DovydasTEDS/teds-kb-100/pcb/kb.kicad_sch

## KiCad design pcb/kb.kicad_sch (2026-01-30)

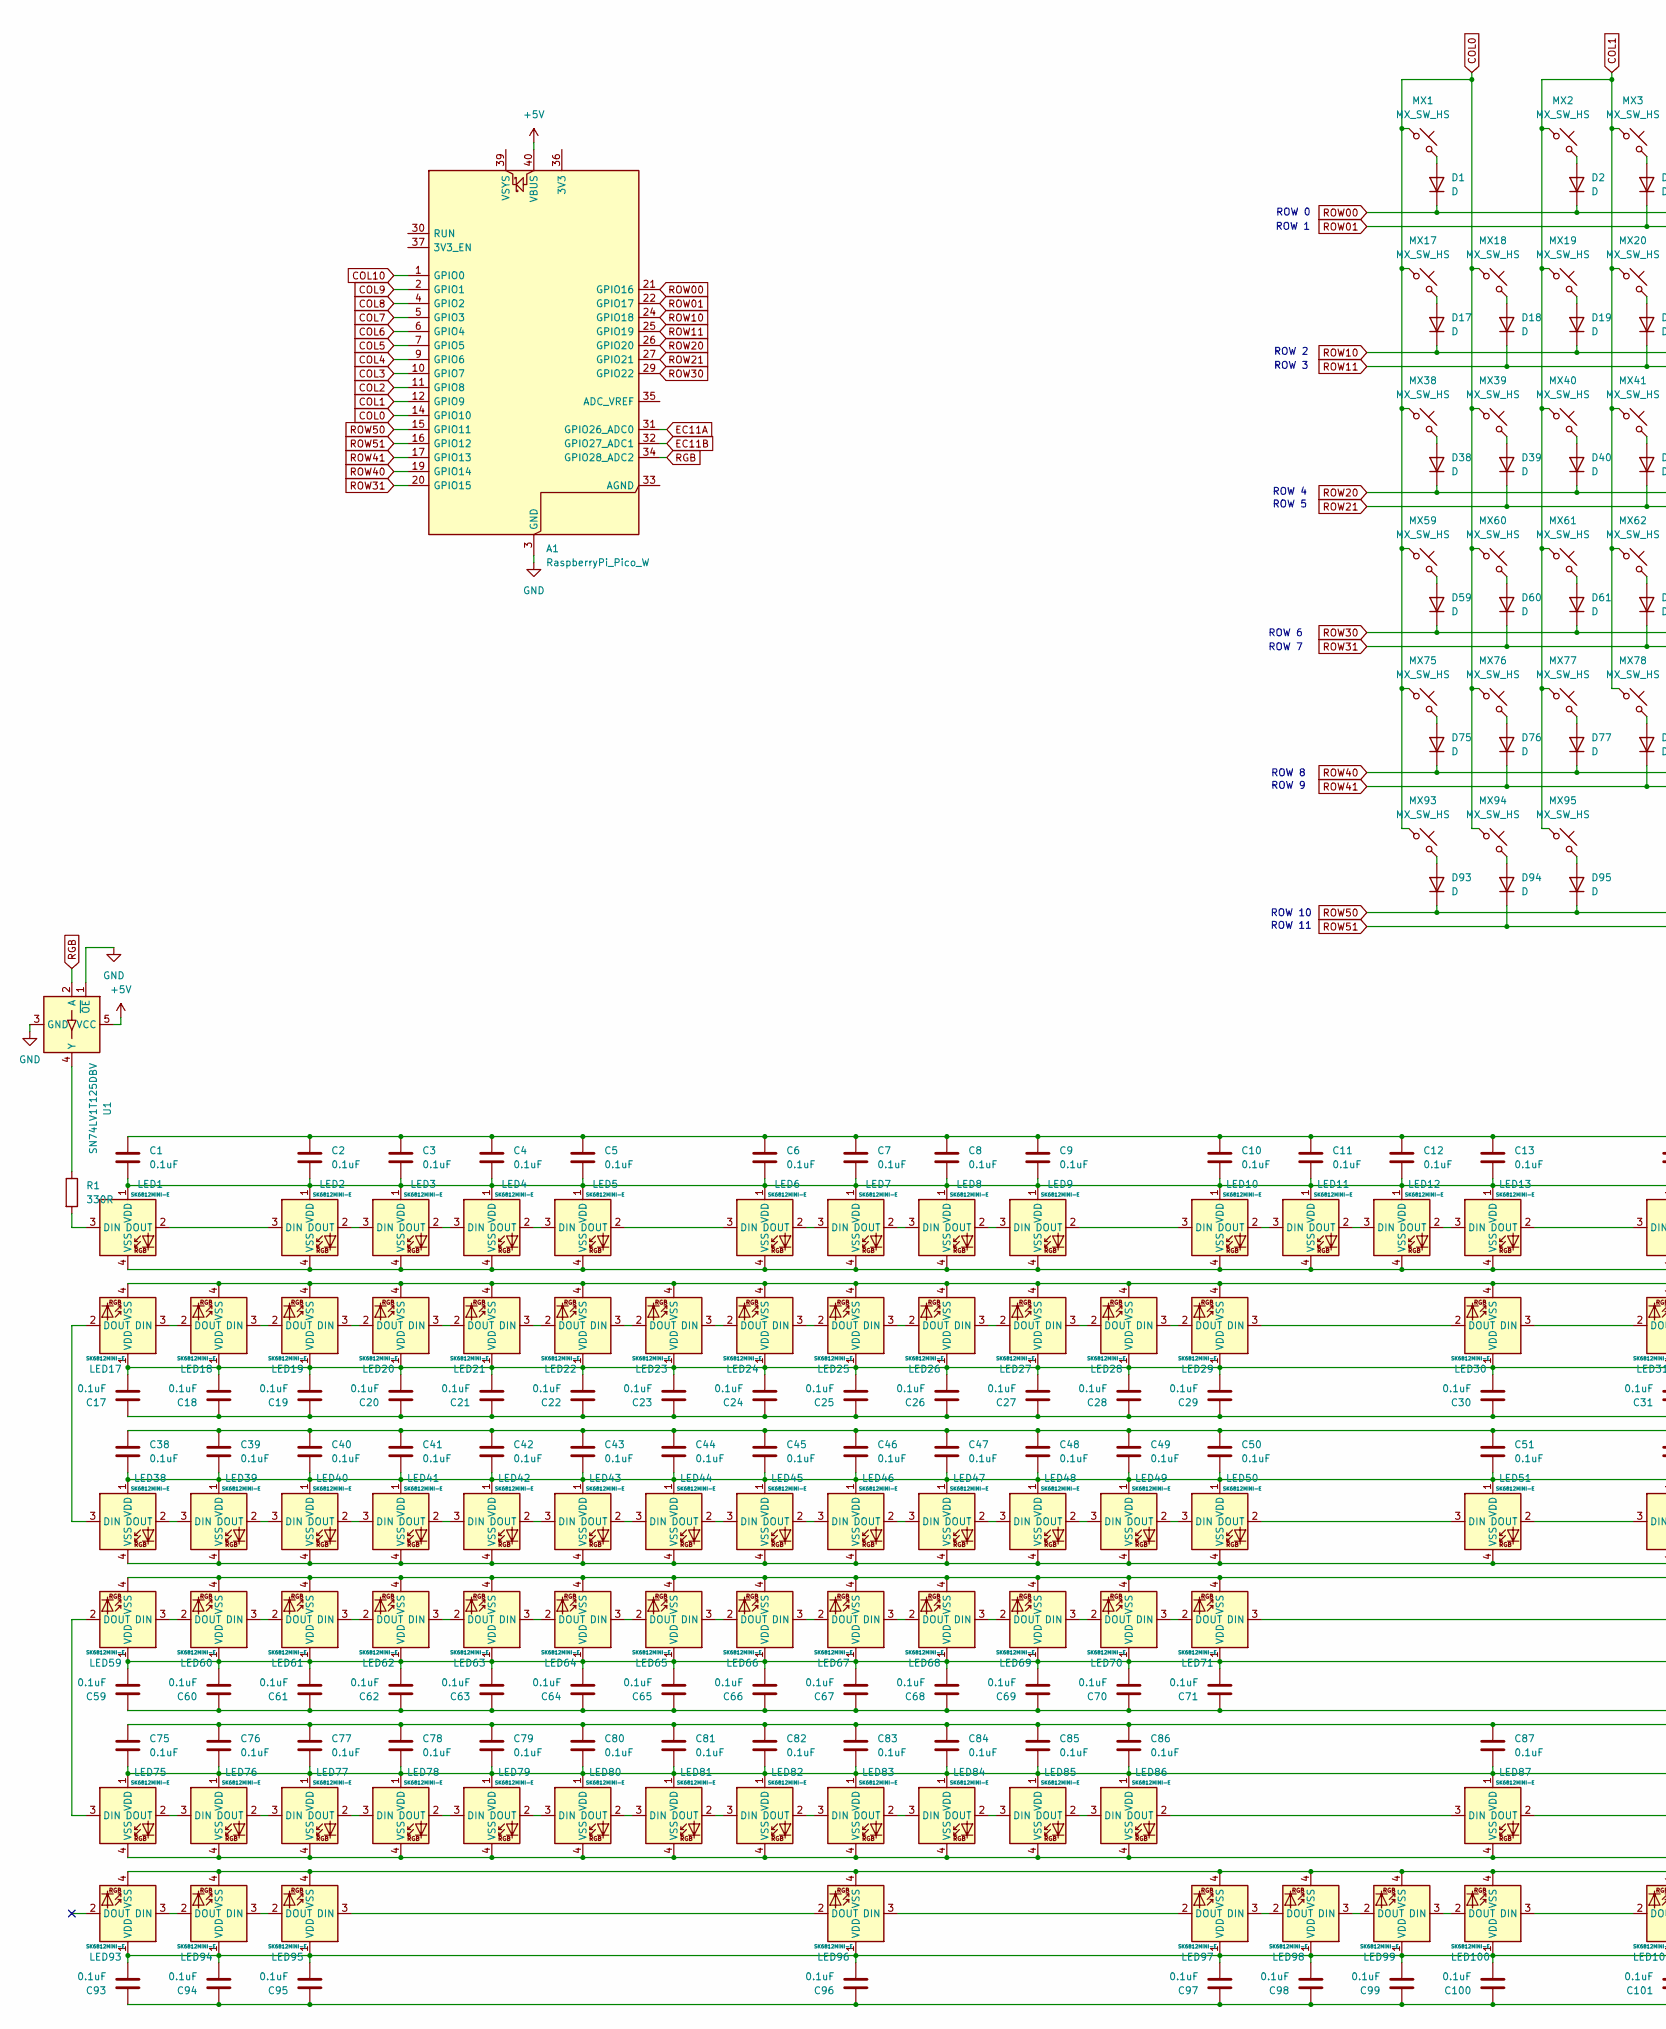
[picture p6: schematic kb.kicad_sch, part in row 1, column 1]

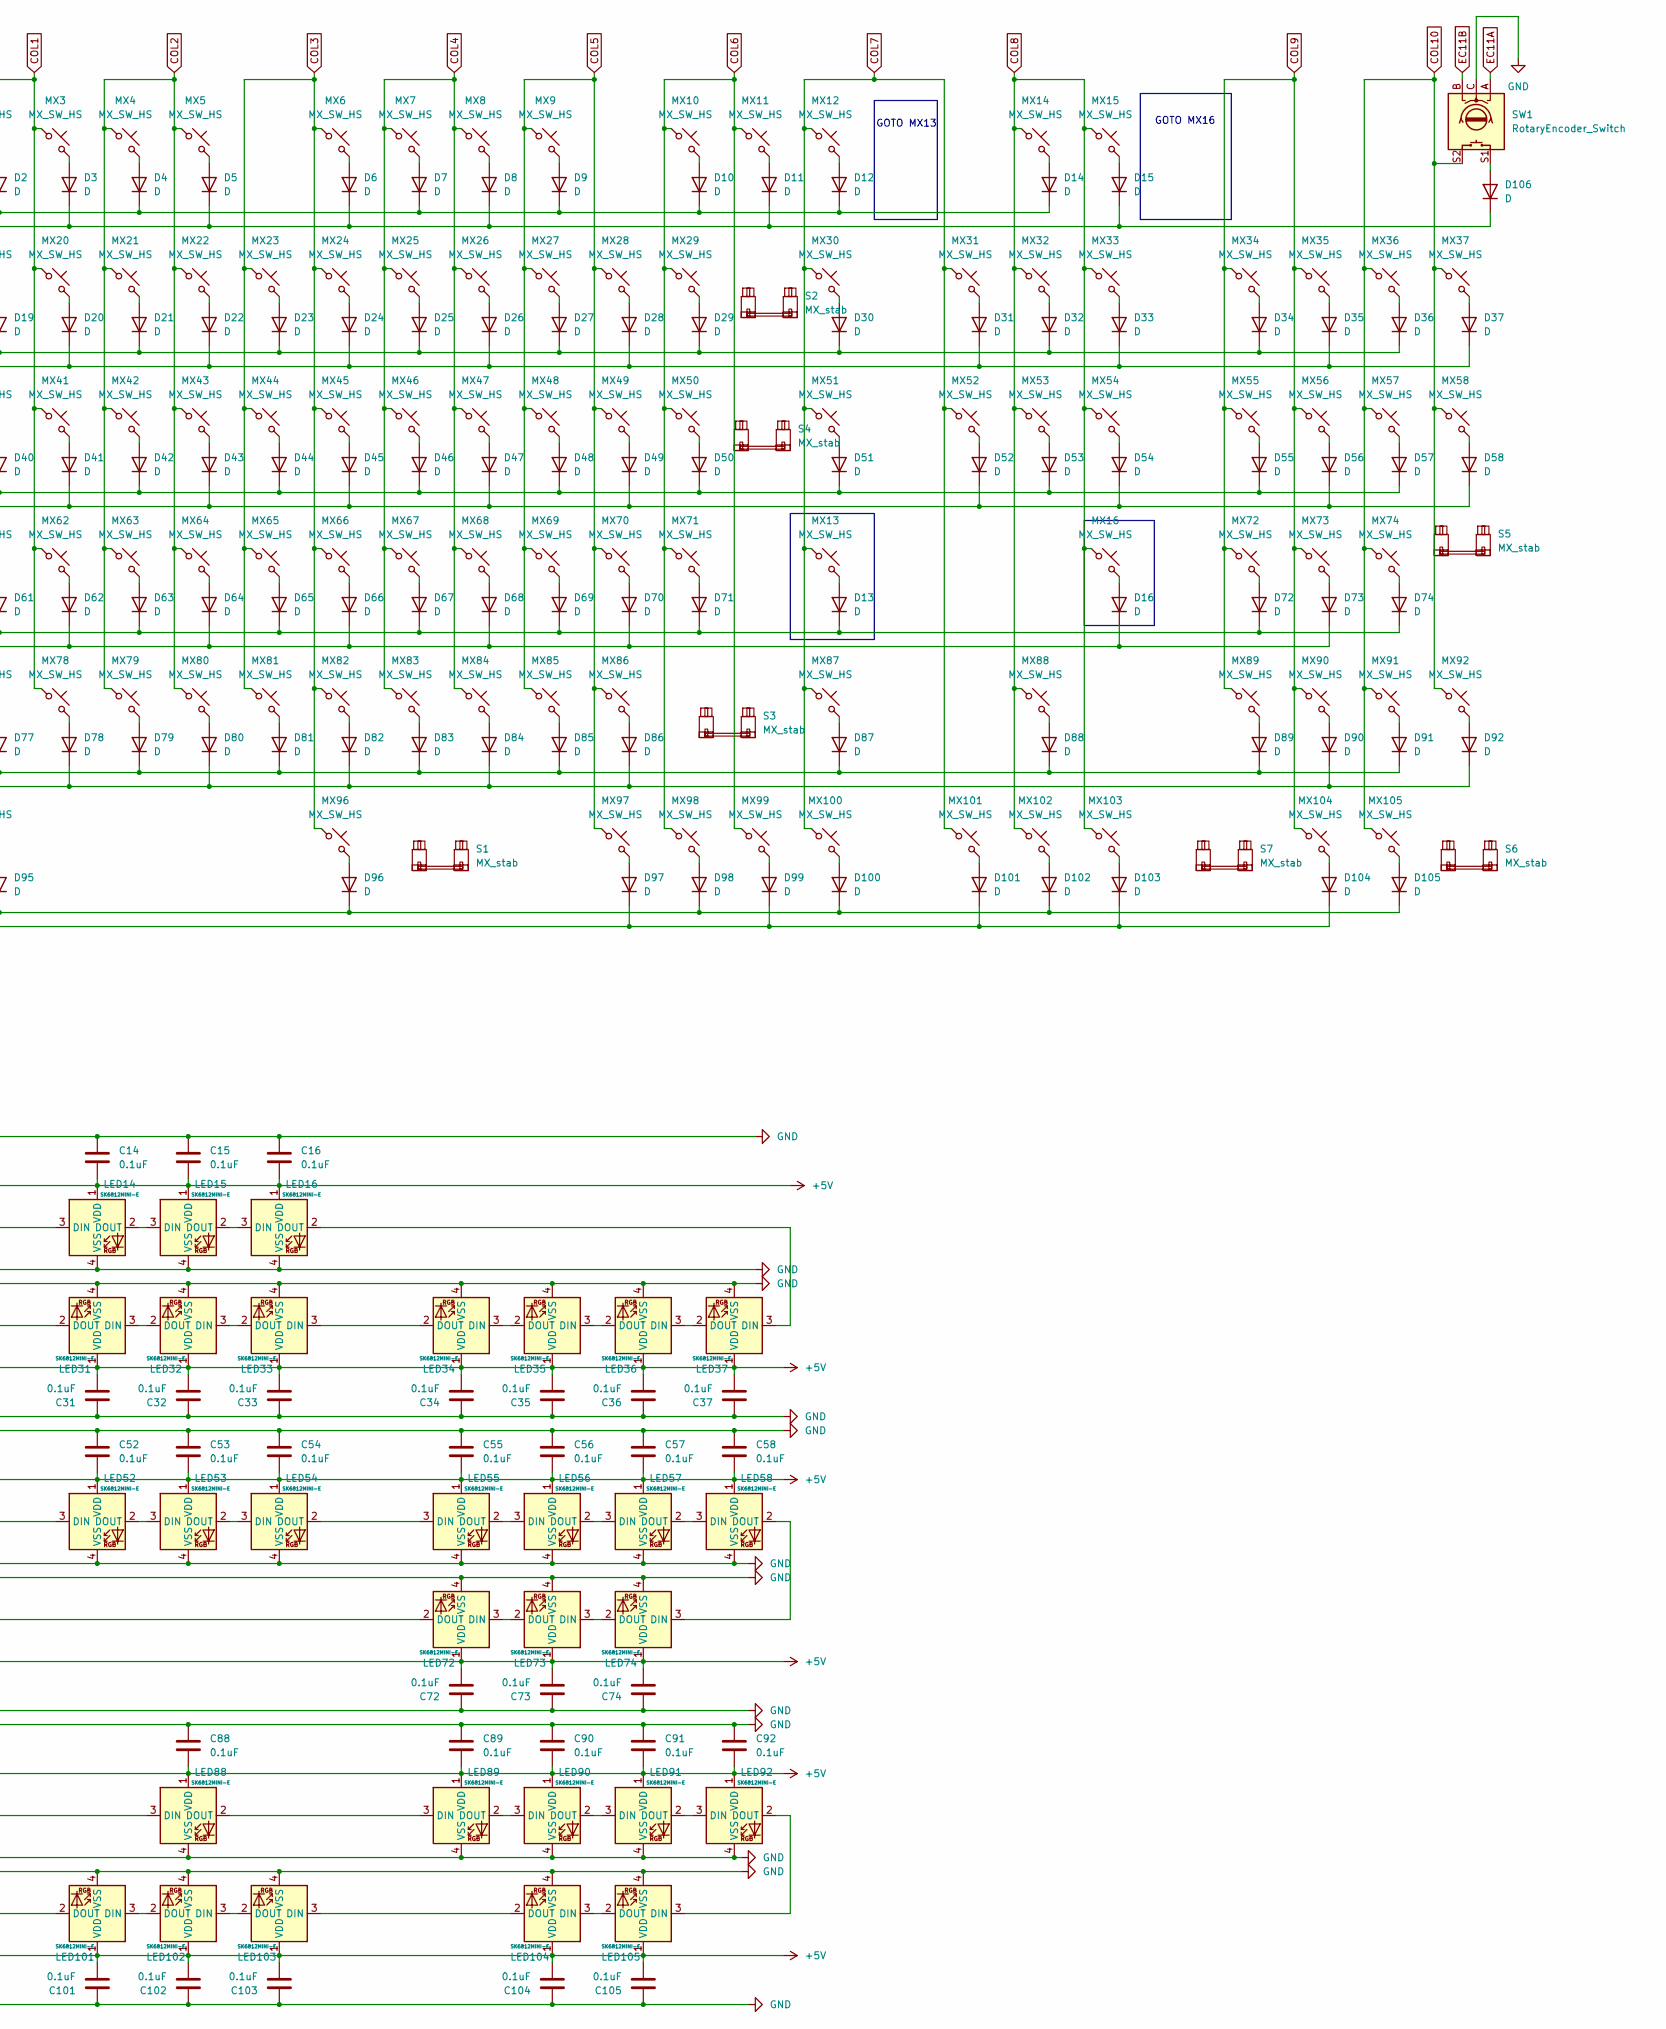
[picture p7: schematic kb.kicad_sch, part in row 1, column 2]

Parts:
A1: RaspberryPi_Pico_W; RaspberryPi_Pico_Common_Unspecified
C1, C2, C3, C4, C5, C6, C7, C8, C9, C10, C11, C12, C13, C14, C15, C16, C17, C18, C19, C20, C21, C22, C23, C24, C25, C26, C27, C28, C29, C30, C31, C32, C33, C34, C35, C36, C37, C38, C39, C40, C41, C42, C43, C44, C45, C46, C47, C48, C49, C50, C51, C52, C53, C54, C55, C56, C57, C58, C59, C60, C61, C62, C63, C64, C65, C66, C67, C68, C69, C70, C71, C72, C73, C74, C75, C76, C77, C78, C79, C80, C81, C82, C83, C84, C85, C86, C87, C88, C89, C90, C91, C92, C93, C94, C95, C96, C97, C98, C99, C100, C101, C102, C103, C104, C105: 0.1uF; C_0805_2012Metric_Pad1.18x1.45mm_HandSolder
D1, D2, D3, D4, D5, D6, D7, D8, D9, D10, D11, D12, D13, D14, D15, D16, D17, D18, D19, D20, D21, D22, D23, D24, D25, D26, D27, D28, D29, D30, D31, D32, D33, D34, D35, D36, D37, D38, D39, D40, D41, D42, D43, D44, D45, D46, D47, D48, D49, D50, D51, D52, D53, D54, D55, D56, D57, D58, D59, D60, D61, D62, D63, D64, D65, D66, D67, D68, D69, D70, D71, D72, D73, D74, D75, D76, D77, D78, D79, D80, D81, D82, D83, D84, D85, D86, D87, D88, D89, D90, D91, D92, D93, D94, D95, D96, D97, D98, D99, D100, D101, D102, D103, D104, D105, D106: D; D_SOD-123
LED1, LED2, LED3, LED4, LED5, LED6, LED7, LED8, LED9, LED10, LED11, LED12, LED13, LED14, LED15, LED16, LED38, LED39, LED40, LED41, LED42, LED43, LED44, LED45, LED46, LED47, LED48, LED49, LED50, LED51, LED52, LED53, LED54, LED55, LED56, LED57, LED75, LED76, LED77, LED78, LED79, LED80, LED81, LED82, LED83, LED84, LED85, LED86, LED87, LED88, LED89, LED90, LED91: SK6812MINI-E; LED_MX_6028R-ROT
LED17, LED18, LED19, LED20, LED21, LED22, LED23, LED24, LED25, LED26, LED27, LED28, LED29, LED30, LED31, LED32, LED33, LED34, LED35, LED36, LED37, LED58, LED59, LED60, LED61, LED62, LED63, LED64, LED65, LED66, LED67, LED68, LED69, LED70, LED71, LED72, LED73, LED74, LED92, LED93, LED94, LED95, LED96, LED97, LED98, LED99, LED100, LED101, LED102, LED103, LED104, LED105: SK6812MINI-E; LED_MX_6028R
MX1, MX2, MX3, MX4, MX5, MX6, MX7, MX8, MX9, MX10, MX11, MX12, MX13, MX14, MX15, MX16, MX17, MX18, MX19, MX20, MX21, MX22, MX23, MX24, MX25, MX26, MX27, MX28, MX29, MX30, MX31, MX32, MX33, MX34, MX35, MX36, MX37, MX39, MX40, MX41, MX42, MX43, MX44, MX45, MX46, MX47, MX48, MX49, MX50, MX51, MX52, MX53, MX54, MX55, MX56, MX57, MX58, MX60, MX61, MX62, MX63, MX64, MX65, MX66, MX67, MX68, MX69, MX70, MX71, MX72, MX73, MX74, MX76, MX77, MX78, MX79, MX80, MX81, MX82, MX83, MX84, MX85, MX86, MX87, MX88, MX89, MX90, MX91, MX92, MX96, MX101, MX102, MX103, MX104, MX105: MX_SW_HS; SW_MX_HS_CPG151101S11_1u
MX38: MX_SW_HS; SW_MX_HS_CPG151101S11_1.5u
MX59: MX_SW_HS; SW_MX_HS_CPG151101S11_1.75u
MX75, MX93, MX94, MX95, MX97, MX98, MX99, MX100: MX_SW_HS; SW_MX_HS_CPG151101S11_1.25u
R1: 330R; R_0805_2012Metric_Pad1.20x1.40mm_HandSolder
S1: MX_stab; STAB_MX_P_6.25u
S2, S5, S6, S7: MX_stab; STAB_MX_2u
S3: MX_stab; STAB_MX_2.75u
S4: MX_stab; STAB_MX_P_ISO
SW1: RotaryEncoder_Switch; ROT_Alps_EC11E-Switch
U1: SN74LV1T125DBV; SOT-23-5_HandSoldering

Connections:
+5V: A1.40 (VBUS), C1.2, C2.2, C3.2, C4.2, C5.2, C6.2, C7.2, C8.2, C9.2, C10.2, C11.2, C12.2, C13.2, C14.2, C15.2, C16.2, C17.2, C18.2, C19.2, C20.2, C21.2, C22.2, C23.2, C24.2, C25.2, C26.2, C27.2, C28.2, C29.2, C30.2, C31.2, C32.2, C33.2, C34.2, C35.2, C36.2, C37.2, C38.2, C39.2, C40.2, C41.2, C42.2, C43.2, C44.2, C45.2, C46.2, C47.2, C48.2, C49.2, C50.2, C51.2, C52.2, C53.2, C54.2, C55.2, C56.2, C57.2, C58.2, C59.2, C60.2, C61.2, C62.2, C63.2, C64.2, C65.2, C66.2, C67.2, C68.2, C69.2, C70.2, C71.2, C72.2, C73.2, C74.2, C75.2, C76.2, C77.2, C78.2, C79.2, C80.2, C81.2, C82.2, C83.2, C84.2, C85.2, C86.2, C87.2, C88.2, C89.2, C90.2, C91.2, C92.2, C93.2, C94.2, C95.2, C96.2, C97.2, C98.2, C99.2, C100.2, C101.2, C102.2, C103.2, C104.2, C105.2, LED1.1 (VDD), LED2.1 (VDD), LED3.1 (VDD), LED4.1 (VDD), LED5.1 (VDD), LED6.1 (VDD), LED7.1 (VDD), LED8.1 (VDD), LED9.1 (VDD), LED10.1 (VDD), LED11.1 (VDD), LED12.1 (VDD), LED13.1 (VDD), LED14.1 (VDD), LED15.1 (VDD), LED16.1 (VDD), LED17.1 (VDD), LED18.1 (VDD), LED19.1 (VDD), LED20.1 (VDD), LED21.1 (VDD), LED22.1 (VDD), LED23.1 (VDD), LED24.1 (VDD), LED25.1 (VDD), LED26.1 (VDD), LED27.1 (VDD), LED28.1 (VDD), LED29.1 (VDD), LED30.1 (VDD), LED31.1 (VDD), LED32.1 (VDD), LED33.1 (VDD), LED34.1 (VDD), LED35.1 (VDD), LED36.1 (VDD), LED37.1 (VDD), LED38.1 (VDD), LED39.1 (VDD), LED40.1 (VDD), LED41.1 (VDD), LED42.1 (VDD), LED43.1 (VDD), LED44.1 (VDD), LED45.1 (VDD), LED46.1 (VDD), LED47.1 (VDD), LED48.1 (VDD), LED49.1 (VDD), LED50.1 (VDD), LED51.1 (VDD), LED52.1 (VDD), LED53.1 (VDD), LED54.1 (VDD), LED55.1 (VDD), LED56.1 (VDD), LED57.1 (VDD), LED58.1 (VDD), LED59.1 (VDD), LED60.1 (VDD), LED61.1 (VDD), LED62.1 (VDD), LED63.1 (VDD), LED64.1 (VDD), LED65.1 (VDD), LED66.1 (VDD), LED67.1 (VDD), LED68.1 (VDD), LED69.1 (VDD), LED70.1 (VDD), LED71.1 (VDD), LED72.1 (VDD), LED73.1 (VDD), LED74.1 (VDD), LED75.1 (VDD), LED76.1 (VDD), LED77.1 (VDD), LED78.1 (VDD), LED79.1 (VDD), LED80.1 (VDD), LED81.1 (VDD), LED82.1 (VDD), LED83.1 (VDD), LED84.1 (VDD), LED85.1 (VDD), LED86.1 (VDD), LED87.1 (VDD), LED88.1 (VDD), LED89.1 (VDD), LED90.1 (VDD), LED91.1 (VDD), LED92.1 (VDD), LED93.1 (VDD), LED94.1 (VDD), LED95.1 (VDD), LED96.1 (VDD), LED97.1 (VDD), LED98.1 (VDD), LED99.1 (VDD), LED100.1 (VDD), LED101.1 (VDD), LED102.1 (VDD), LED103.1 (VDD), LED104.1 (VDD), LED105.1 (VDD), U1.5 (VCC)
COL0: A1.14 (GPIO10), MX1.1, MX17.1, MX18.1, MX38.1, MX39.1, MX59.1, MX60.1, MX75.1, MX76.1, MX93.1, MX94.1
COL1: A1.12 (GPIO9), MX2.1, MX3.1, MX19.1, MX20.1, MX40.1, MX41.1, MX61.1, MX62.1, MX77.1, MX78.1, MX95.1
COL2: A1.11 (GPIO8), MX4.1, MX5.1, MX21.1, MX22.1, MX42.1, MX43.1, MX63.1, MX64.1, MX79.1, MX80.1
COL3: A1.10 (GPIO7), MX6.1, MX23.1, MX24.1, MX44.1, MX45.1, MX65.1, MX66.1, MX81.1, MX82.1, MX96.1
COL4: A1.9 (GPIO6), MX7.1, MX8.1, MX25.1, MX26.1, MX46.1, MX47.1, MX67.1, MX68.1, MX83.1, MX84.1
COL5: A1.7 (GPIO5), MX9.1, MX27.1, MX28.1, MX48.1, MX49.1, MX69.1, MX70.1, MX85.1, MX86.1, MX97.1
COL6: A1.6 (GPIO4), MX10.1, MX11.1, MX29.1, MX50.1, MX71.1, MX98.1, MX99.1
COL7: A1.5 (GPIO3), MX12.1, MX13.1, MX30.1, MX31.1, MX51.1, MX52.1, MX87.1, MX100.1, MX101.1
COL8: A1.4 (GPIO2), MX14.1, MX15.1, MX16.1, MX32.1, MX33.1, MX53.1, MX54.1, MX88.1, MX102.1, MX103.1
COL9: A1.2 (GPIO1), MX34.1, MX35.1, MX55.1, MX56.1, MX72.1, MX73.1, MX89.1, MX90.1, MX104.1
COL10: A1.1 (GPIO0), MX36.1, MX37.1, MX57.1, MX58.1, MX74.1, MX91.1, MX92.1, MX105.1, SW1.S2
EC11A: A1.31 (GPIO26_ADC0), SW1.A
EC11B: A1.32 (GPIO27_ADC1), SW1.B
GND: A1.3 (GND), A1.8 (GND), A1.13 (GND), A1.18 (GND), A1.23 (GND), A1.28 (GND), A1.38 (GND), C1.1, C2.1, C3.1, C4.1, C5.1, C6.1, C7.1, C8.1, C9.1, C10.1, C11.1, C12.1, C13.1, C14.1, C15.1, C16.1, C17.1, C18.1, C19.1, C20.1, C21.1, C22.1, C23.1, C24.1, C25.1, C26.1, C27.1, C28.1, C29.1, C30.1, C31.1, C32.1, C33.1, C34.1, C35.1, C36.1, C37.1, C38.1, C39.1, C40.1, C41.1, C42.1, C43.1, C44.1, C45.1, C46.1, C47.1, C48.1, C49.1, C50.1, C51.1, C52.1, C53.1, C54.1, C55.1, C56.1, C57.1, C58.1, C59.1, C60.1, C61.1, C62.1, C63.1, C64.1, C65.1, C66.1, C67.1, C68.1, C69.1, C70.1, C71.1, C72.1, C73.1, C74.1, C75.1, C76.1, C77.1, C78.1, C79.1, C80.1, C81.1, C82.1, C83.1, C84.1, C85.1, C86.1, C87.1, C88.1, C89.1, C90.1, C91.1, C92.1, C93.1, C94.1, C95.1, C96.1, C97.1, C98.1, C99.1, C100.1, C101.1, C102.1, C103.1, C104.1, C105.1, LED1.4 (VSS), LED2.4 (VSS), LED3.4 (VSS), LED4.4 (VSS), LED5.4 (VSS), LED6.4 (VSS), LED7.4 (VSS), LED8.4 (VSS), LED9.4 (VSS), LED10.4 (VSS), LED11.4 (VSS), LED12.4 (VSS), LED13.4 (VSS), LED14.4 (VSS), LED15.4 (VSS), LED16.4 (VSS), LED17.4 (VSS), LED18.4 (VSS), LED19.4 (VSS), LED20.4 (VSS), LED21.4 (VSS), LED22.4 (VSS), LED23.4 (VSS), LED24.4 (VSS), LED25.4 (VSS), LED26.4 (VSS), LED27.4 (VSS), LED28.4 (VSS), LED29.4 (VSS), LED30.4 (VSS), LED31.4 (VSS), LED32.4 (VSS), LED33.4 (VSS), LED34.4 (VSS), LED35.4 (VSS), LED36.4 (VSS), LED37.4 (VSS), LED38.4 (VSS), LED39.4 (VSS), LED40.4 (VSS), LED41.4 (VSS), LED42.4 (VSS), LED43.4 (VSS), LED44.4 (VSS), LED45.4 (VSS), LED46.4 (VSS), LED47.4 (VSS), LED48.4 (VSS), LED49.4 (VSS), LED50.4 (VSS), LED51.4 (VSS), LED52.4 (VSS), LED53.4 (VSS), LED54.4 (VSS), LED55.4 (VSS), LED56.4 (VSS), LED57.4 (VSS), LED58.4 (VSS), LED59.4 (VSS), LED60.4 (VSS), LED61.4 (VSS), LED62.4 (VSS), LED63.4 (VSS), LED64.4 (VSS), LED65.4 (VSS), LED66.4 (VSS), LED67.4 (VSS), LED68.4 (VSS), LED69.4 (VSS), LED70.4 (VSS), LED71.4 (VSS), LED72.4 (VSS), LED73.4 (VSS), LED74.4 (VSS), LED75.4 (VSS), LED76.4 (VSS), LED77.4 (VSS), LED78.4 (VSS), LED79.4 (VSS), LED80.4 (VSS), LED81.4 (VSS), LED82.4 (VSS), LED83.4 (VSS), LED84.4 (VSS), LED85.4 (VSS), LED86.4 (VSS), LED87.4 (VSS), LED88.4 (VSS), LED89.4 (VSS), LED90.4 (VSS), LED91.4 (VSS), LED92.4 (VSS), LED93.4 (VSS), LED94.4 (VSS), LED95.4 (VSS), LED96.4 (VSS), LED97.4 (VSS), LED98.4 (VSS), LED99.4 (VSS), LED100.4 (VSS), LED101.4 (VSS), LED102.4 (VSS), LED103.4 (VSS), LED104.4 (VSS), LED105.4 (VSS), SW1.C, U1.1 (~OE), U1.3 (GND)
unnamed: D1.2 (A), MX1.2
unnamed: D2.2 (A), MX2.2
unnamed: D3.2 (A), MX3.2
unnamed: D4.2 (A), MX4.2
unnamed: D5.2 (A), MX5.2
unnamed: D6.2 (A), MX6.2
unnamed: D7.2 (A), MX7.2
unnamed: D8.2 (A), MX8.2
unnamed: D9.2 (A), MX9.2
unnamed: D10.2 (A), MX10.2
unnamed: D11.2 (A), MX11.2
unnamed: D12.2 (A), MX12.2
unnamed: D13.2 (A), MX13.2
unnamed: D14.2 (A), MX14.2
unnamed: D15.2 (A), MX15.2
unnamed: D16.2 (A), MX16.2
unnamed: D17.2 (A), MX17.2
unnamed: D18.2 (A), MX18.2
unnamed: D19.2 (A), MX19.2
unnamed: D20.2 (A), MX20.2
unnamed: D21.2 (A), MX21.2
unnamed: D22.2 (A), MX22.2
unnamed: D23.2 (A), MX23.2
unnamed: D24.2 (A), MX24.2
unnamed: D25.2 (A), MX25.2
unnamed: D26.2 (A), MX26.2
unnamed: D27.2 (A), MX27.2
unnamed: D28.2 (A), MX28.2
unnamed: D29.2 (A), MX29.2
unnamed: D30.2 (A), MX30.2
unnamed: D31.2 (A), MX31.2
unnamed: D32.2 (A), MX32.2
unnamed: D33.2 (A), MX33.2
unnamed: D34.2 (A), MX34.2
unnamed: D35.2 (A), MX35.2
unnamed: D36.2 (A), MX36.2
unnamed: D37.2 (A), MX37.2
unnamed: D38.2 (A), MX38.2
unnamed: D39.2 (A), MX39.2
unnamed: D40.2 (A), MX40.2
unnamed: D41.2 (A), MX41.2
unnamed: D42.2 (A), MX42.2
unnamed: D43.2 (A), MX43.2
unnamed: D44.2 (A), MX44.2
unnamed: D45.2 (A), MX45.2
unnamed: D46.2 (A), MX46.2
unnamed: D47.2 (A), MX47.2
unnamed: D48.2 (A), MX48.2
unnamed: D49.2 (A), MX49.2
unnamed: D50.2 (A), MX50.2
unnamed: D51.2 (A), MX51.2
unnamed: D52.2 (A), MX52.2
unnamed: D53.2 (A), MX53.2
unnamed: D54.2 (A), MX54.2
unnamed: D55.2 (A), MX55.2
unnamed: D56.2 (A), MX56.2
unnamed: D57.2 (A), MX57.2
unnamed: D58.2 (A), MX58.2
unnamed: D59.2 (A), MX59.2
unnamed: D60.2 (A), MX60.2
unnamed: D61.2 (A), MX61.2
unnamed: D62.2 (A), MX62.2
unnamed: D63.2 (A), MX63.2
unnamed: D64.2 (A), MX64.2
unnamed: D65.2 (A), MX65.2
unnamed: D66.2 (A), MX66.2
unnamed: D67.2 (A), MX67.2
unnamed: D68.2 (A), MX68.2
unnamed: D69.2 (A), MX69.2
unnamed: D70.2 (A), MX70.2
unnamed: D71.2 (A), MX71.2
unnamed: D72.2 (A), MX72.2
unnamed: D73.2 (A), MX73.2
unnamed: D74.2 (A), MX74.2
unnamed: D75.2 (A), MX75.2
unnamed: D76.2 (A), MX76.2
unnamed: D77.2 (A), MX77.2
unnamed: D78.2 (A), MX78.2
unnamed: D79.2 (A), MX79.2
unnamed: D80.2 (A), MX80.2
unnamed: D81.2 (A), MX81.2
unnamed: D82.2 (A), MX82.2
unnamed: D83.2 (A), MX83.2
unnamed: D84.2 (A), MX84.2
unnamed: D85.2 (A), MX85.2
unnamed: D86.2 (A), MX86.2
unnamed: D87.2 (A), MX87.2
unnamed: D88.2 (A), MX88.2
unnamed: D89.2 (A), MX89.2
unnamed: D90.2 (A), MX90.2
unnamed: D91.2 (A), MX91.2
unnamed: D92.2 (A), MX92.2
unnamed: D93.2 (A), MX93.2
unnamed: D94.2 (A), MX94.2
unnamed: D95.2 (A), MX95.2
unnamed: D96.2 (A), MX96.2
unnamed: D97.2 (A), MX97.2
unnamed: D98.2 (A), MX98.2
unnamed: D99.2 (A), MX99.2
unnamed: D100.2 (A), MX100.2
unnamed: D101.2 (A), MX101.2
unnamed: D102.2 (A), MX102.2
unnamed: D103.2 (A), MX103.2
unnamed: D104.2 (A), MX104.2
unnamed: D105.2 (A), MX105.2
unnamed: D106.2 (A), SW1.S1
unnamed: LED1.2 (DOUT), LED2.3 (DIN)
unnamed: LED1.3 (DIN), R1.2
unnamed: LED2.2 (DOUT), LED3.3 (DIN)
unnamed: LED3.2 (DOUT), LED4.3 (DIN)
unnamed: LED4.2 (DOUT), LED5.3 (DIN)
unnamed: LED5.2 (DOUT), LED6.3 (DIN)
unnamed: LED6.2 (DOUT), LED7.3 (DIN)
unnamed: LED7.2 (DOUT), LED8.3 (DIN)
unnamed: LED8.2 (DOUT), LED9.3 (DIN)
unnamed: LED10.2 (DOUT), LED11.3 (DIN)
unnamed: LED9.2 (DOUT), LED10.3 (DIN)
unnamed: LED11.2 (DOUT), LED12.3 (DIN)
unnamed: LED12.2 (DOUT), LED13.3 (DIN)
unnamed: LED13.2 (DOUT), LED14.3 (DIN)
unnamed: LED14.2 (DOUT), LED15.3 (DIN)
unnamed: LED15.2 (DOUT), LED16.3 (DIN)
unnamed: LED16.2 (DOUT), LED37.3 (DIN)
unnamed: LED17.2 (DOUT), LED38.3 (DIN)
unnamed: LED17.3 (DIN), LED18.2 (DOUT)
unnamed: LED18.3 (DIN), LED19.2 (DOUT)
unnamed: LED19.3 (DIN), LED20.2 (DOUT)
unnamed: LED20.3 (DIN), LED21.2 (DOUT)
unnamed: LED21.3 (DIN), LED22.2 (DOUT)
unnamed: LED22.3 (DIN), LED23.2 (DOUT)
unnamed: LED23.3 (DIN), LED24.2 (DOUT)
unnamed: LED24.3 (DIN), LED25.2 (DOUT)
unnamed: LED25.3 (DIN), LED26.2 (DOUT)
unnamed: LED26.3 (DIN), LED27.2 (DOUT)
unnamed: LED27.3 (DIN), LED28.2 (DOUT)
unnamed: LED28.3 (DIN), LED29.2 (DOUT)
unnamed: LED29.3 (DIN), LED30.2 (DOUT)
unnamed: LED30.3 (DIN), LED31.2 (DOUT)
unnamed: LED31.3 (DIN), LED32.2 (DOUT)
unnamed: LED32.3 (DIN), LED33.2 (DOUT)
unnamed: LED33.3 (DIN), LED34.2 (DOUT)
unnamed: LED34.3 (DIN), LED35.2 (DOUT)
unnamed: LED35.3 (DIN), LED36.2 (DOUT)
unnamed: LED36.3 (DIN), LED37.2 (DOUT)
unnamed: LED38.2 (DOUT), LED39.3 (DIN)
unnamed: LED39.2 (DOUT), LED40.3 (DIN)
unnamed: LED40.2 (DOUT), LED41.3 (DIN)
unnamed: LED41.2 (DOUT), LED42.3 (DIN)
unnamed: LED42.2 (DOUT), LED43.3 (DIN)
unnamed: LED43.2 (DOUT), LED44.3 (DIN)
unnamed: LED44.2 (DOUT), LED45.3 (DIN)
unnamed: LED45.2 (DOUT), LED46.3 (DIN)
unnamed: LED46.2 (DOUT), LED47.3 (DIN)
unnamed: LED47.2 (DOUT), LED48.3 (DIN)
unnamed: LED48.2 (DOUT), LED49.3 (DIN)
unnamed: LED49.2 (DOUT), LED50.3 (DIN)
unnamed: LED50.2 (DOUT), LED51.3 (DIN)
unnamed: LED51.2 (DOUT), LED52.3 (DIN)
unnamed: LED52.2 (DOUT), LED53.3 (DIN)
unnamed: LED53.2 (DOUT), LED54.3 (DIN)
unnamed: LED54.2 (DOUT), LED55.3 (DIN)
unnamed: LED55.2 (DOUT), LED56.3 (DIN)
unnamed: LED56.2 (DOUT), LED57.3 (DIN)
unnamed: LED57.2 (DOUT), LED58.3 (DIN)
unnamed: LED58.2 (DOUT), LED74.3 (DIN)
unnamed: LED59.2 (DOUT), LED75.3 (DIN)
unnamed: LED59.3 (DIN), LED60.2 (DOUT)
unnamed: LED60.3 (DIN), LED61.2 (DOUT)
unnamed: LED61.3 (DIN), LED62.2 (DOUT)
unnamed: LED62.3 (DIN), LED63.2 (DOUT)
unnamed: LED63.3 (DIN), LED64.2 (DOUT)
unnamed: LED64.3 (DIN), LED65.2 (DOUT)
unnamed: LED65.3 (DIN), LED66.2 (DOUT)
unnamed: LED66.3 (DIN), LED67.2 (DOUT)
unnamed: LED67.3 (DIN), LED68.2 (DOUT)
unnamed: LED68.3 (DIN), LED69.2 (DOUT)
unnamed: LED69.3 (DIN), LED70.2 (DOUT)
unnamed: LED70.3 (DIN), LED71.2 (DOUT)
unnamed: LED71.3 (DIN), LED72.2 (DOUT)
unnamed: LED72.3 (DIN), LED73.2 (DOUT)
unnamed: LED73.3 (DIN), LED74.2 (DOUT)
unnamed: LED75.2 (DOUT), LED76.3 (DIN)
unnamed: LED76.2 (DOUT), LED77.3 (DIN)
unnamed: LED77.2 (DOUT), LED78.3 (DIN)
unnamed: LED78.2 (DOUT), LED79.3 (DIN)
unnamed: LED79.2 (DOUT), LED80.3 (DIN)
unnamed: LED80.2 (DOUT), LED81.3 (DIN)
unnamed: LED81.2 (DOUT), LED82.3 (DIN)
unnamed: LED82.2 (DOUT), LED83.3 (DIN)
unnamed: LED83.2 (DOUT), LED84.3 (DIN)
unnamed: LED84.2 (DOUT), LED85.3 (DIN)
unnamed: LED85.2 (DOUT), LED86.3 (DIN)
unnamed: LED86.2 (DOUT), LED87.3 (DIN)
unnamed: LED87.2 (DOUT), LED88.3 (DIN)
unnamed: LED88.2 (DOUT), LED89.3 (DIN)
unnamed: LED89.2 (DOUT), LED90.3 (DIN)
unnamed: LED90.2 (DOUT), LED91.3 (DIN)
unnamed: LED91.2 (DOUT), LED92.3 (DIN)
unnamed: LED93.3 (DIN), LED94.2 (DOUT)
unnamed: LED94.3 (DIN), LED95.2 (DOUT)
unnamed: LED95.3 (DIN), LED96.2 (DOUT)
unnamed: LED96.3 (DIN), LED97.2 (DOUT)
unnamed: LED97.3 (DIN), LED98.2 (DOUT)
unnamed: LED98.3 (DIN), LED99.2 (DOUT)
unnamed: LED99.3 (DIN), LED100.2 (DOUT)
unnamed: LED100.3 (DIN), LED101.2 (DOUT)
unnamed: LED101.3 (DIN), LED102.2 (DOUT)
unnamed: LED102.3 (DIN), LED103.2 (DOUT)
unnamed: LED103.3 (DIN), LED104.2 (DOUT)
unnamed: LED104.3 (DIN), LED105.2 (DOUT)
unnamed: LED92.2 (DOUT), LED105.3 (DIN)
unnamed: R1.1, U1.4 (Y)
RGB: A1.34 (GPIO28_ADC2), U1.2 (A)
ROW00: A1.21 (GPIO16), D1.1 (K), D2.1 (K), D4.1 (K), D7.1 (K), D9.1 (K), D10.1 (K), D12.1 (K), D14.1 (K)
ROW01: A1.22 (GPIO17), D3.1 (K), D5.1 (K), D6.1 (K), D8.1 (K), D11.1 (K), D15.1 (K), D106.1 (K)
ROW10: A1.24 (GPIO18), D17.1 (K), D19.1 (K), D21.1 (K), D23.1 (K), D25.1 (K), D27.1 (K), D29.1 (K), D30.1 (K), D32.1 (K), D34.1 (K), D36.1 (K)
ROW11: A1.25 (GPIO19), D18.1 (K), D20.1 (K), D22.1 (K), D24.1 (K), D26.1 (K), D28.1 (K), D31.1 (K), D33.1 (K), D35.1 (K), D37.1 (K)
ROW20: A1.26 (GPIO20), D38.1 (K), D40.1 (K), D42.1 (K), D44.1 (K), D46.1 (K), D48.1 (K), D50.1 (K), D51.1 (K), D53.1 (K), D55.1 (K), D57.1 (K)
ROW21: A1.27 (GPIO21), D39.1 (K), D41.1 (K), D43.1 (K), D45.1 (K), D47.1 (K), D49.1 (K), D52.1 (K), D54.1 (K), D56.1 (K), D58.1 (K)
ROW30: A1.29 (GPIO22), D13.1 (K), D59.1 (K), D61.1 (K), D63.1 (K), D65.1 (K), D67.1 (K), D69.1 (K), D71.1 (K), D72.1 (K), D74.1 (K)
ROW31: A1.20 (GPIO15), D16.1 (K), D60.1 (K), D62.1 (K), D64.1 (K), D66.1 (K), D68.1 (K), D70.1 (K), D73.1 (K)
ROW40: A1.19 (GPIO14), D75.1 (K), D77.1 (K), D79.1 (K), D81.1 (K), D83.1 (K), D85.1 (K), D87.1 (K), D88.1 (K), D89.1 (K), D91.1 (K)
ROW41: A1.17 (GPIO13), D76.1 (K), D78.1 (K), D80.1 (K), D82.1 (K), D84.1 (K), D86.1 (K), D90.1 (K), D92.1 (K)
ROW50: A1.15 (GPIO11), D93.1 (K), D95.1 (K), D96.1 (K), D98.1 (K), D100.1 (K), D102.1 (K), D105.1 (K)
ROW51: A1.16 (GPIO12), D94.1 (K), D97.1 (K), D99.1 (K), D101.1 (K), D103.1 (K), D104.1 (K)

Notes on the sheet:
ROW 8
ROW 7
ROW 10
ROW 5
GOTO MX13
ROW 0
ROW 6
GOTO MX16
ROW 2
ROW 1
ROW 3
ROW 11
ROW 9
ROW 4
